Beirdo/kegerator-sensors/firmware/temperature-sensor/local.h

#ifndef _local_h_
#define _local_h_

#include "common.h"

/* Macros */

/* Types */

/* Externals */

/* Prototypes */
void tcn75a_setup(void);
uint16_t tcn75a_read( uint8_t regnum );

#endif

/*
 * vim:ts=4:sw=4:ai:et:si:sts=4
 */
